copyrights/b-car/doc/latex/knightrider_8h__incl.pdf

knightrider.h

config.h

Arduino.h Adafruit_NeoPixel.h
