copyrights/b-car/doc/latex/knightrider_8ino__incl.pdf

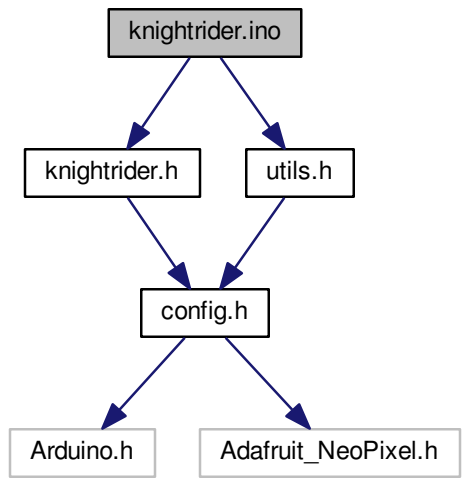
[picture p22: figure]
knightrider.ino; knightrider.h; utils.h; config.h; Arduino.h; Adafruit_NeoPixel.h
