copyrights/b-car/doc/latex/police_8h__incl.pdf

police.h

config.h

Arduino.h Adafruit_NeoPixel.h
