copyrights/b-car/doc/latex/police_8ino__incl.pdf

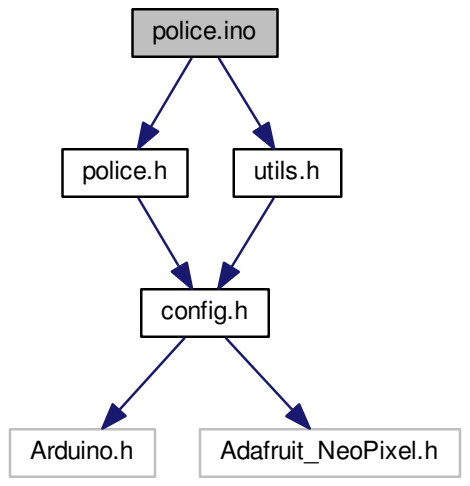
[picture p23: figure]
police.ino; police.h; utils.h; config.h; Arduino.h; Adafruit_NeoPixel.h
