copyrights/b-car/doc/latex/rainbow_8h__incl.pdf

rainbow.h

config.h

Arduino.h Adafruit_NeoPixel.h
