copyrights/b-car/doc/latex/rainbow_8ino__incl.pdf

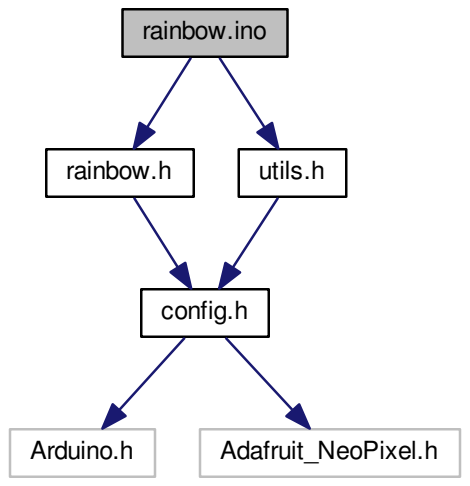
[picture p24: figure]
rainbow.ino; rainbow.h; utils.h; config.h; Arduino.h; Adafruit_NeoPixel.h
