copyrights/b-car/doc/latex/speed_8h__incl.pdf

speed.h

config.h

Arduino.h Adafruit_NeoPixel.h
