copyrights/b-car/doc/latex/speed_8ino__incl.pdf

speed.ino

speed.h

config.h

Arduino.h Adafruit_NeoPixel.h
