copyrights/b-car/doc/latex/utils_8h__incl.pdf

utils.h

config.h

Arduino.h Adafruit_NeoPixel.h
