copyrights/b-car/doc/latex/utils_8ino__incl.pdf

utils.ino

utils.h

config.h

Arduino.h Adafruit_NeoPixel.h
