copyrights/b-car/doc/latex/utils_8h__dep__incl.pdf

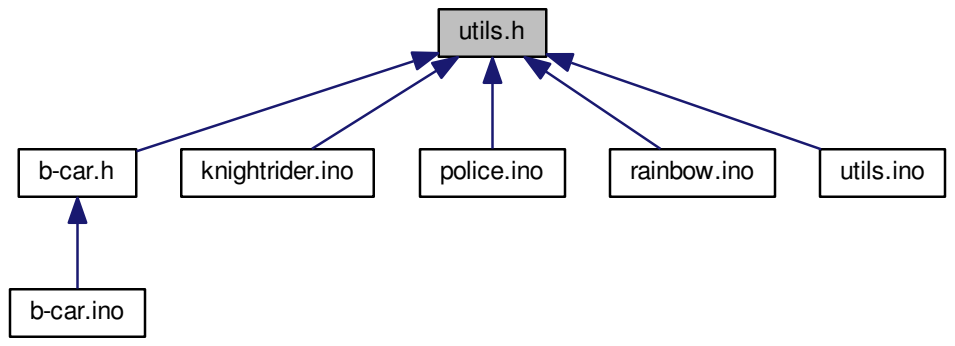
[picture p40: figure]
utils.h; b-car.h; knightrider.ino; police.ino; rainbow.ino; utils.ino; b-car.ino
