copyrights/b-car/src/b-car/b-car.h

#ifndef BCARH
#define BCARH

#include "config.h"
#include "utils.h"
#include "speed.h"
#include "buttons.h"
#include "car_basics.h"
#include "knightrider.h"
#include "police.h"
#include "rainbow.h"

void normalmode();

#endif
